Codezombie23/Bolt-Sniper/Print Files/OpticsRail/Optics Mount Lower.3mf

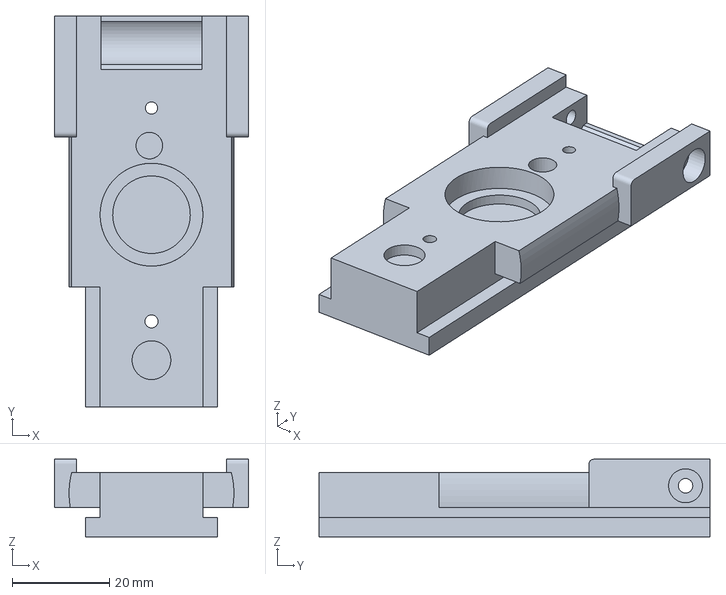
[picture p27: CAD file, 2025-10-11]
Print Files/OpticsRail/Optics Mount Lower.3mf
40.0 x 80.5 x 16.0 mm
