Codezombie23/Bolt-Sniper/Print Files/Receiver/Reciever RHS Double.3mf

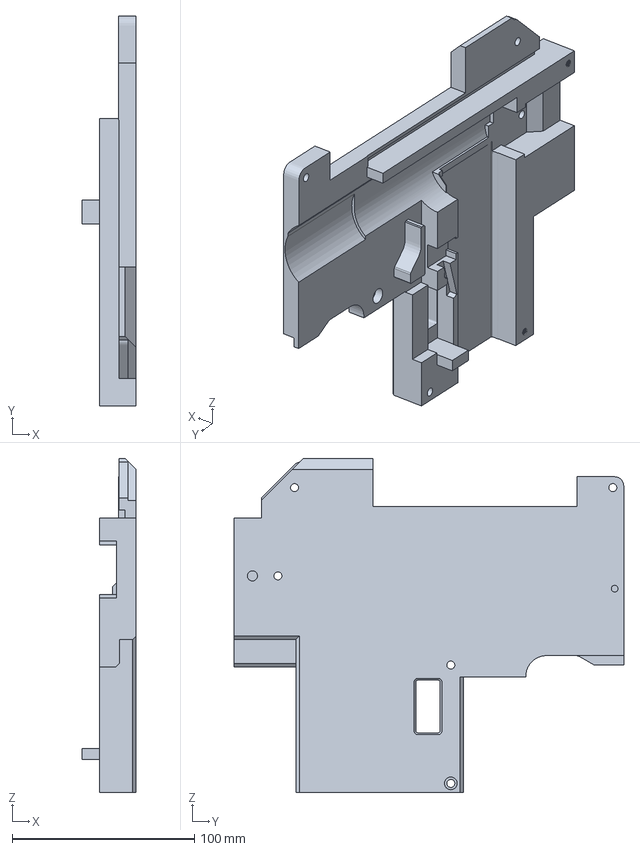
[picture p28: CAD file, 2025-10-11]
Print Files/Receiver/Reciever RHS Double.3mf
29.8 x 214.0 x 183.5 mm
