Codezombie23/Bolt-Sniper/Print Files/Shell/Stock.3mf

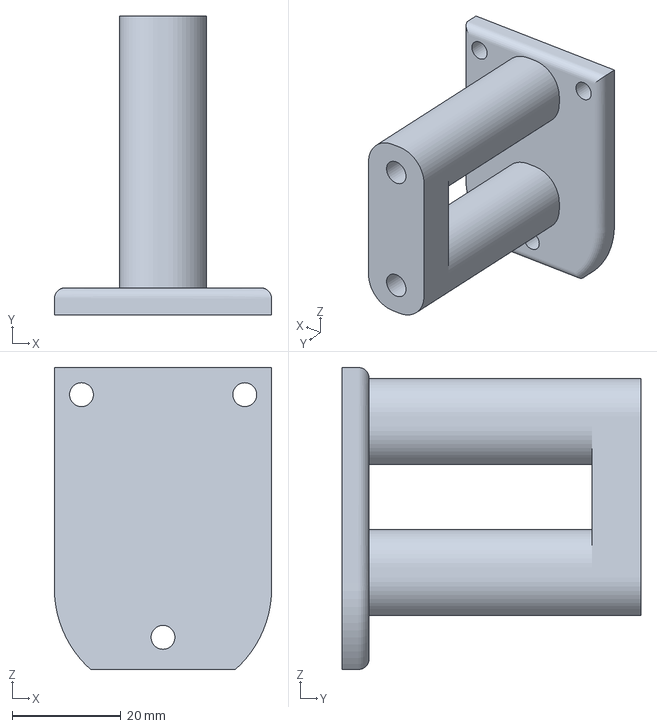
[picture p29: CAD file, 2025-10-11]
Print Files/Shell/Stock.3mf
40.0 x 55.0 x 55.6 mm
