Codezombie23/Bolt-Sniper/Print Files/Trigger Group/GripLHS (STG-44).3mf

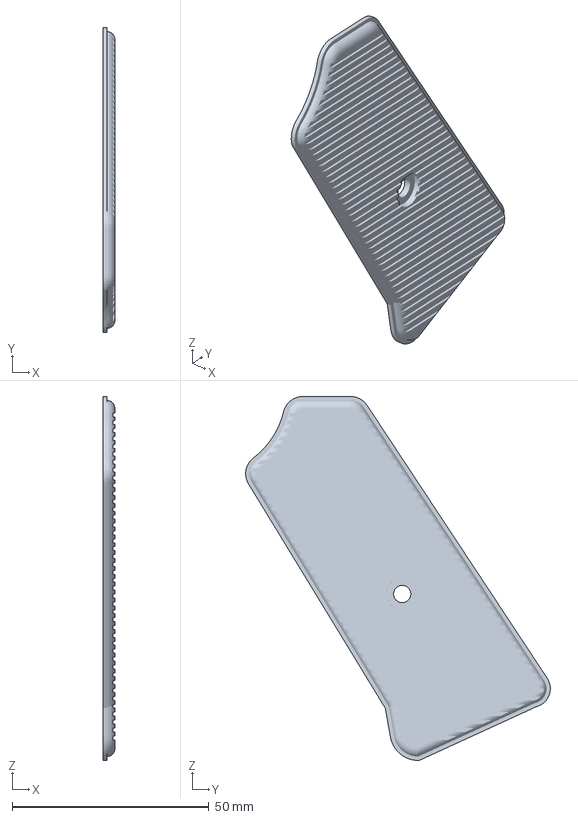
[picture p30: CAD file, 2025-10-06]
Print Files/Trigger Group/GripLHS (STG-44).3mf
3.00 x 77.4 x 92.4 mm
