Codezombie23/Bolt-Sniper/Print Files/Barrel Shroud/Barrel Shroud Front.3mf

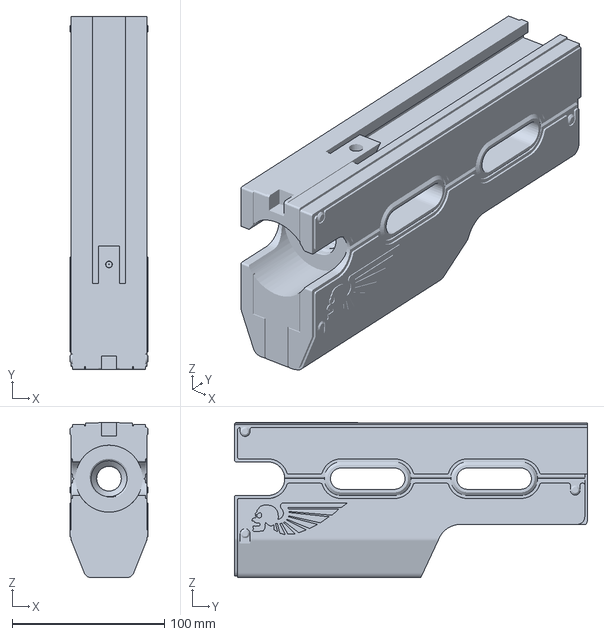
[picture p31: CAD file, 2025-10-11]
Print Files/Barrel Shroud/Barrel Shroud Front.3mf
51.0 x 231.8 x 102.0 mm
