Codezombie23/Bolt-Sniper/Print Files/Internals/Piston for 37 L1.3mf

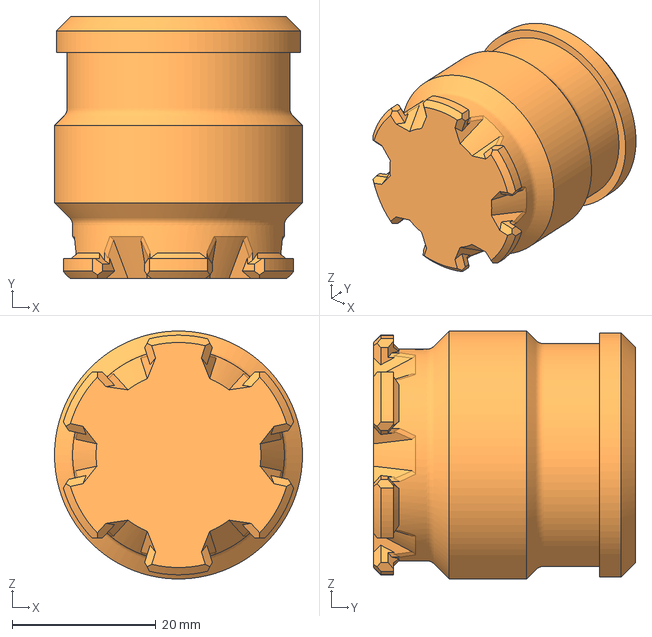
[picture p32: CAD file, 2025-10-11]
Print Files/Internals/Piston for 37 L1.3mf
34.5 x 36.5 x 34.5 mm
