Codezombie23/Bolt-Sniper/Print Files/OpticsRail/Solid OpticsMount.3mf

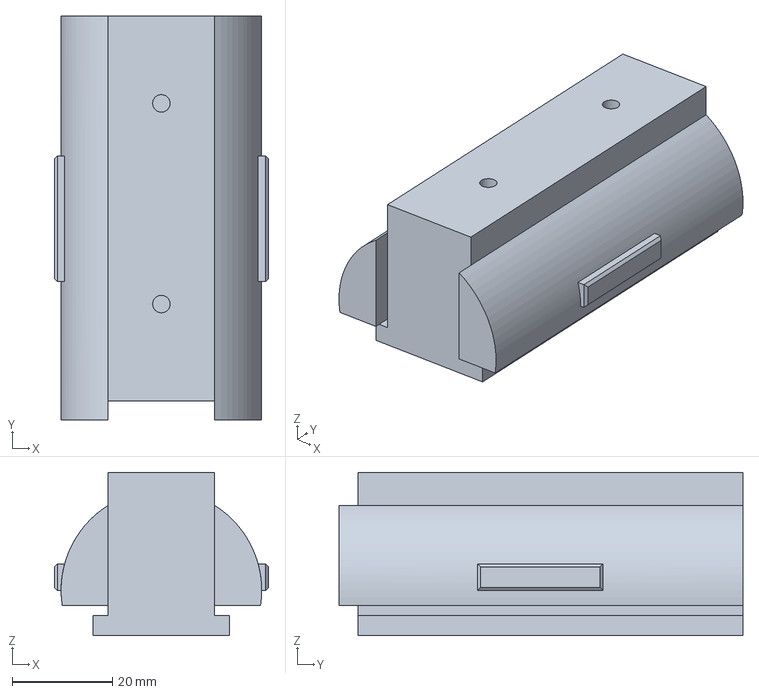
[picture p33: CAD file, 2025-10-11]
Print Files/OpticsRail/Solid OpticsMount.3mf
42.8 x 80.5 x 32.5 mm
