Codezombie23/Bolt-Sniper/Print Files/Trigger Group/Fire Group Frame Right.3mf

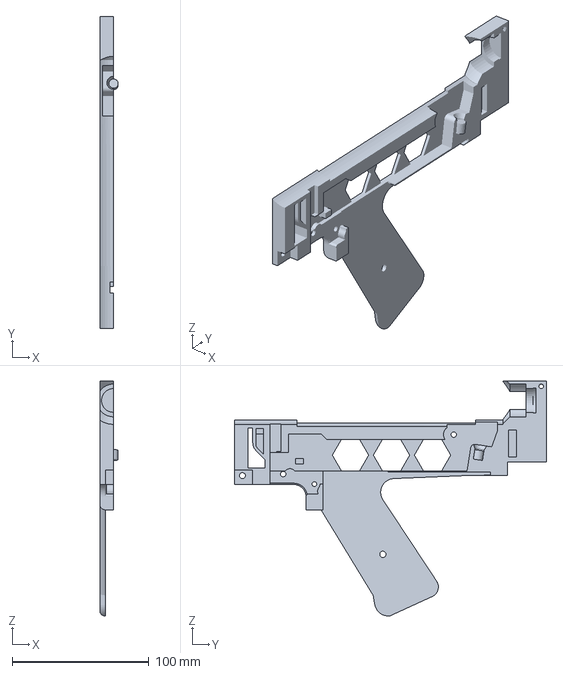
[picture p35: CAD file, 2025-10-06]
Print Files/Trigger Group/Fire Group Frame Right.3mf
13.5 x 228.5 x 171.8 mm
