Codezombie23/Bolt-Sniper/Print Files/Internals/RearShell.3mf

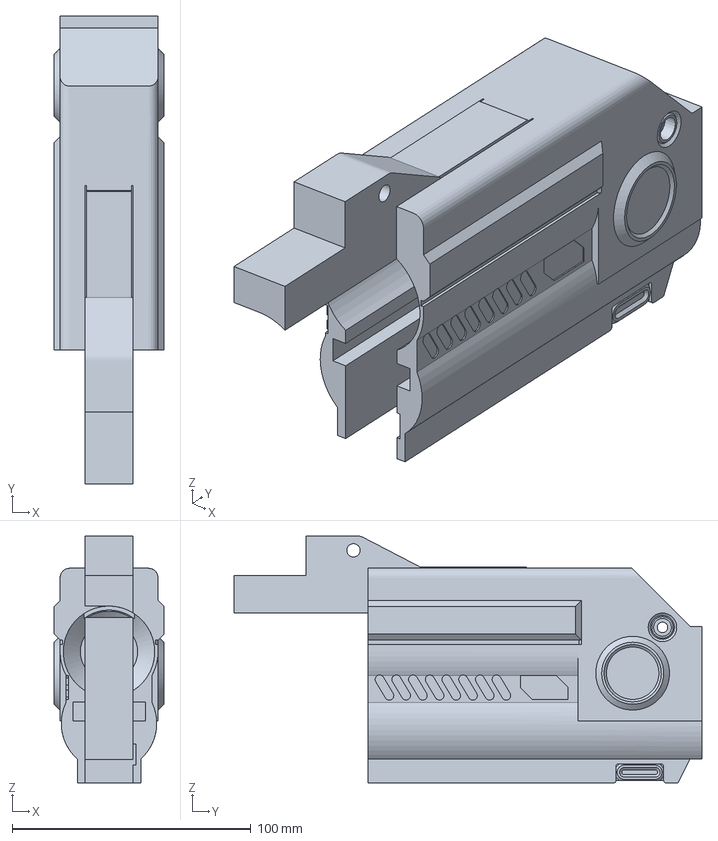
[picture p36: CAD file, 2025-10-11]
Print Files/Internals/RearShell.3mf
46.0 x 196.0 x 103.5 mm
