Codezombie23/Bolt-Sniper/Print Files/OpticsRail/Optics Thumb Wheel.3mf

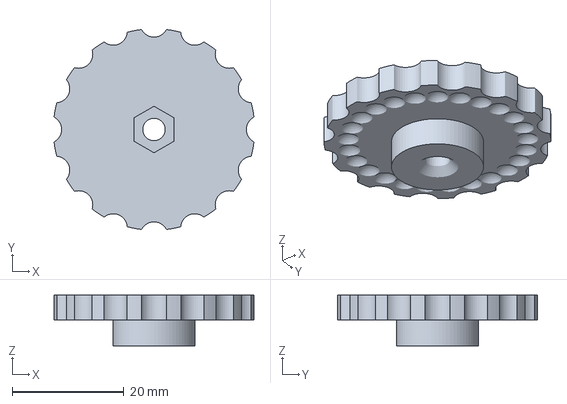
[picture p37: CAD file, 2025-10-11]
Print Files/OpticsRail/Optics Thumb Wheel.3mf
35.7 x 35.7 x 9.10 mm
