Codezombie23/Bolt-Sniper/Print Files/Receiver/Mag Release Internal.3mf

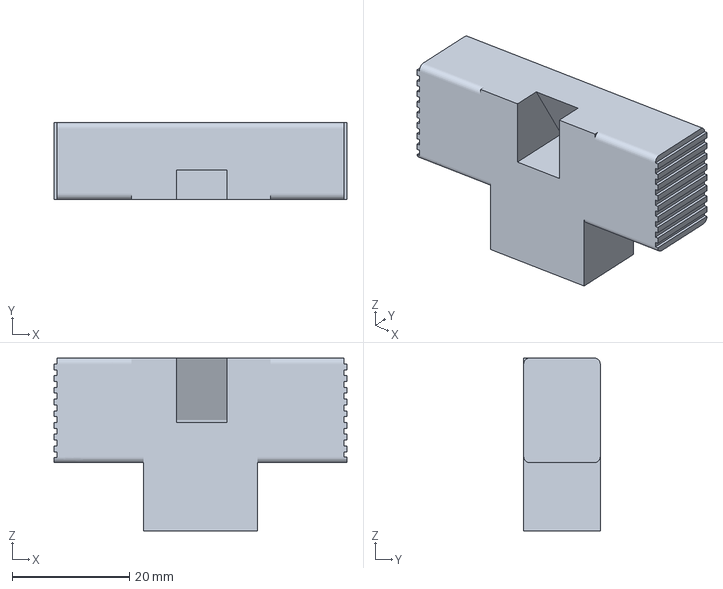
[picture p38: CAD file, 2025-10-11]
Print Files/Receiver/Mag Release Internal.3mf
50.0 x 13.1 x 29.5 mm
