Codezombie23/Bolt-Sniper/Print Files/Shell/Grip Connector.3mf

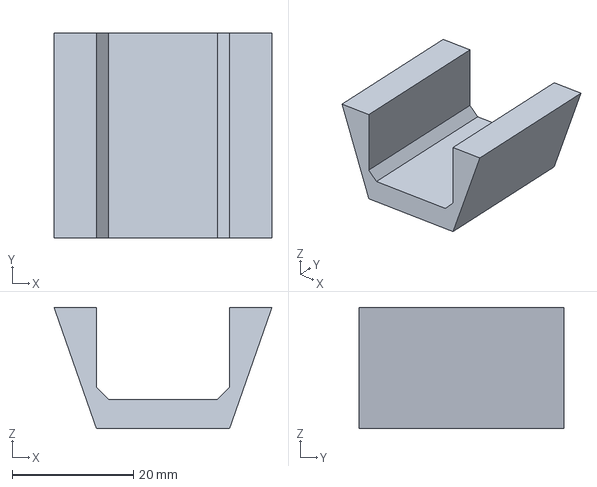
[picture p39: CAD file, 2025-10-11]
Print Files/Shell/Grip Connector.3mf
36.0 x 33.8 x 20.0 mm
