Codezombie23/Bolt-Sniper/Print Files/Trigger Group/Grip Frame.3mf

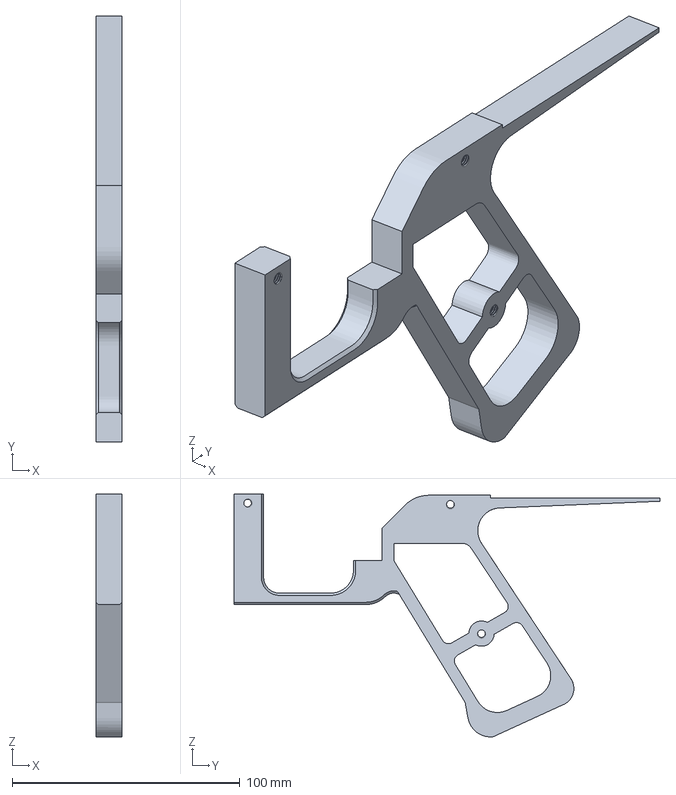
[picture p40: CAD file, 2025-10-06]
Print Files/Trigger Group/Grip Frame.3mf
11.2 x 187.0 x 106.6 mm
