Codezombie23/Bolt-Sniper/Print Files/Internals/Charging Handle.3mf

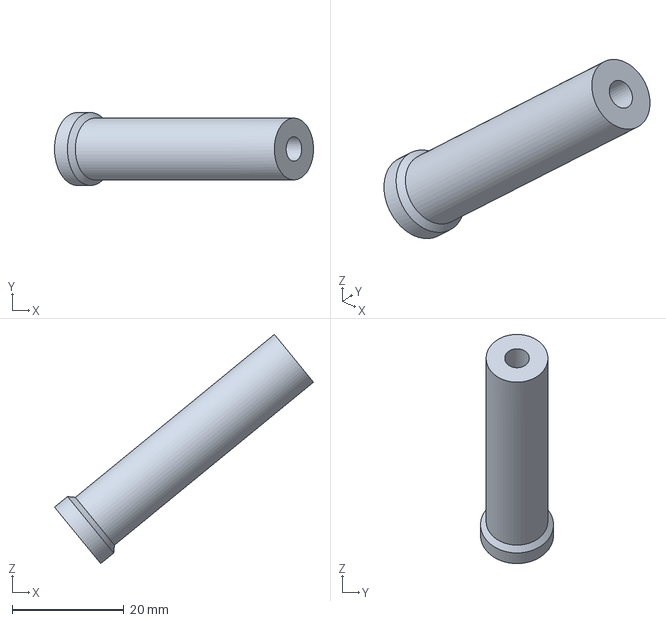
[picture p41: CAD file, 2025-10-11]
Print Files/Internals/Charging Handle.3mf
46.3 x 13.1 x 41.0 mm
