Codezombie23/Bolt-Sniper/Print Files/OpticsRail/Optics Mount Upper.3mf

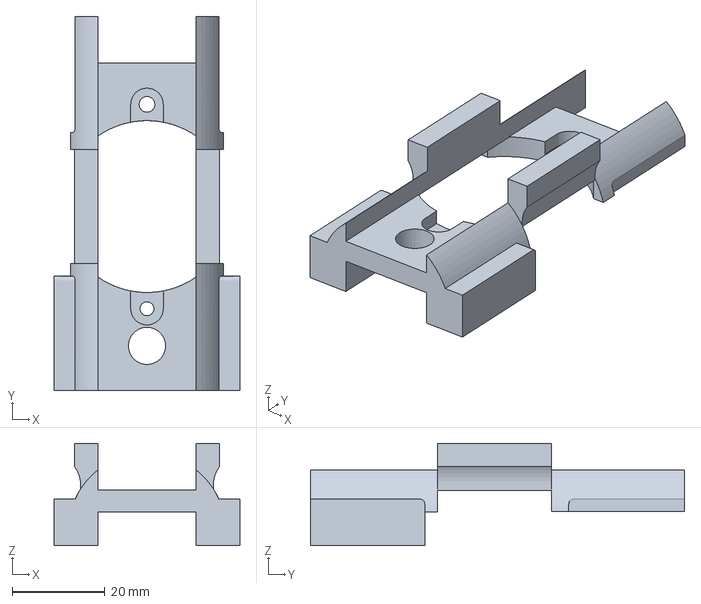
[picture p42: CAD file, 2025-10-11]
Print Files/OpticsRail/Optics Mount Upper.3mf
40.0 x 80.5 x 22.0 mm
