Codezombie23/Bolt-Sniper/Print Files/Receiver/Reciever LHS Double.3mf

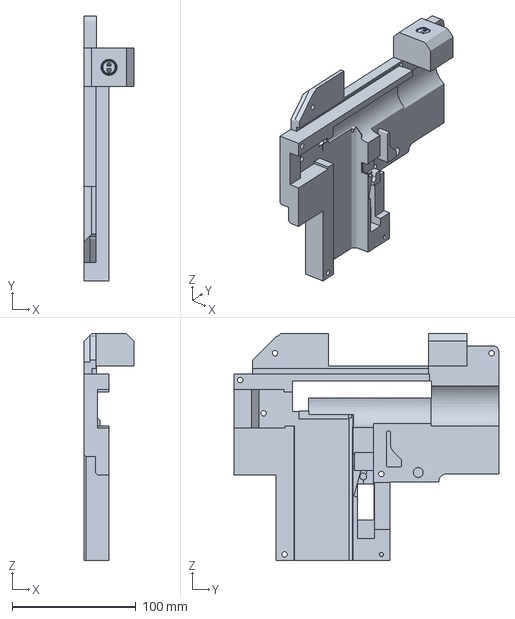
[picture p43: CAD file, 2025-10-11]
Print Files/Receiver/Reciever LHS Double.3mf
40.0 x 214.0 x 183.5 mm
