Codezombie23/Bolt-Sniper/Print Files/Shell/SidePanel LHS.3mf

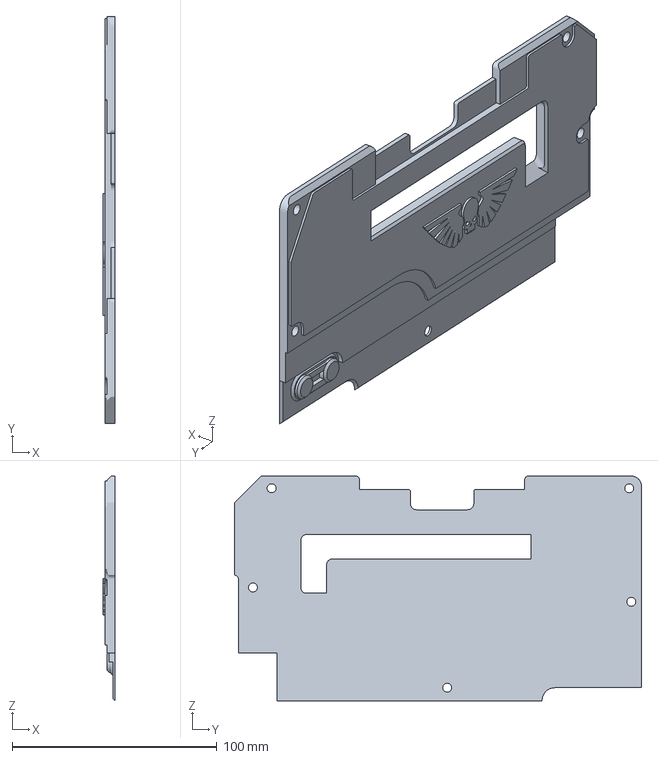
[picture p44: CAD file, 2025-10-11]
Print Files/Shell/SidePanel LHS.3mf
6.00 x 199.0 x 110.0 mm
