Codezombie23/Bolt-Sniper/Print Files/Trigger Group/Grip Locator.3mf

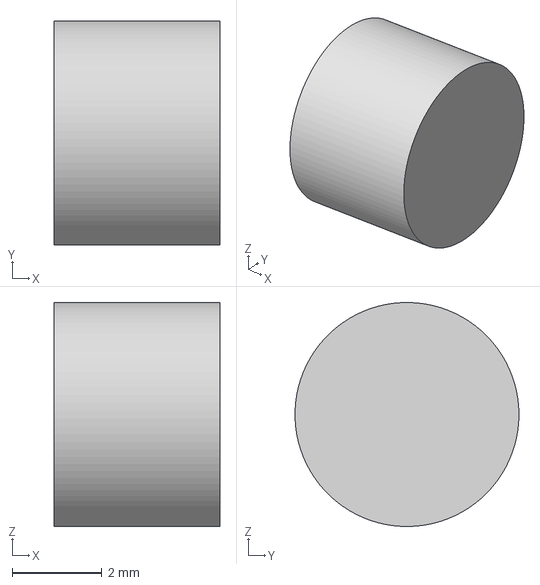
[picture p45: CAD file, 2025-10-06]
Print Files/Trigger Group/Grip Locator.3mf
3.70 x 5.00 x 5.00 mm
