Codezombie23/Bolt-Sniper/Print Files/OpticsRail/Locator.3mf

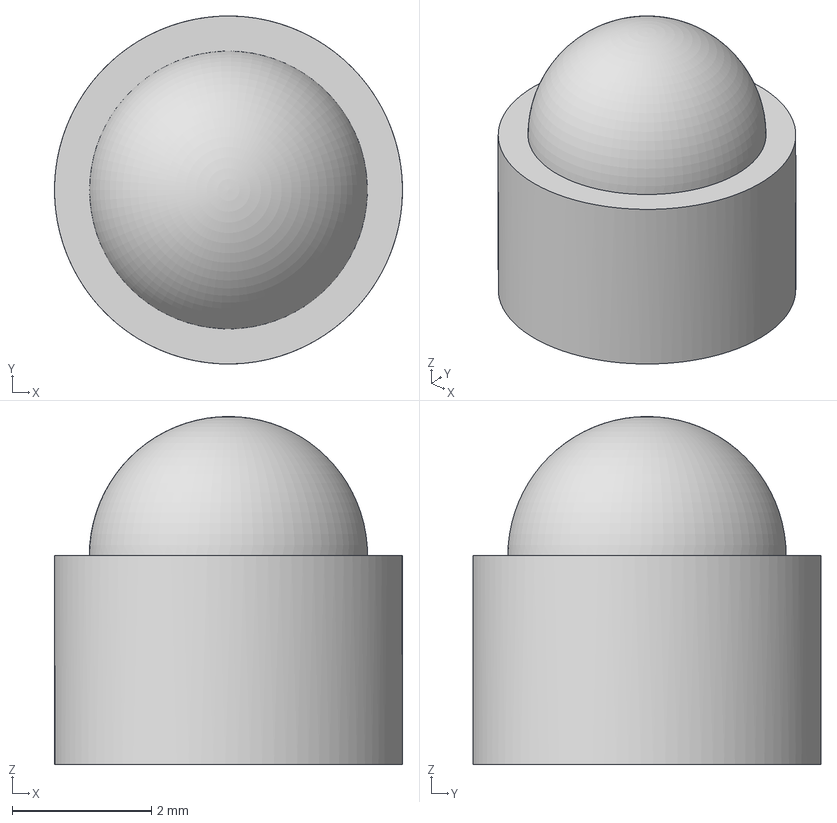
[picture p46: CAD file, 2025-10-11]
Print Files/OpticsRail/Locator.3mf
5.00 x 5.00 x 5.00 mm
