Codezombie23/Bolt-Sniper/Print Files/Receiver/MagReleaseBarDouble.3mf

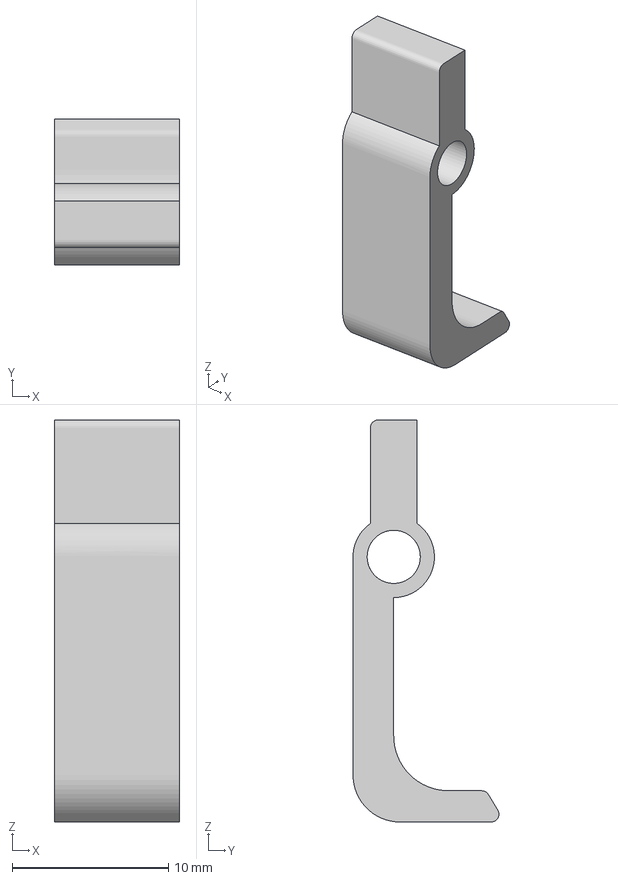
[picture p47: CAD file, 2025-10-11]
Print Files/Receiver/MagReleaseBarDouble.3mf
8.00 x 9.33 x 25.7 mm
