Codezombie23/Bolt-Sniper/Print Files/Trigger Group/Spring Holder.3mf

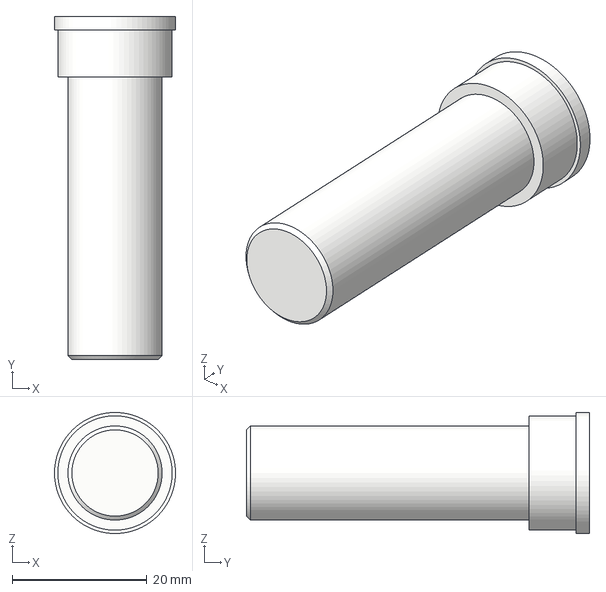
[picture p48: CAD file, 2025-10-06]
Print Files/Trigger Group/Spring Holder.3mf
18.0 x 51.0 x 18.0 mm
