Codezombie23/Bolt-Sniper/Print Files/Trigger Group/TransferBar.3mf

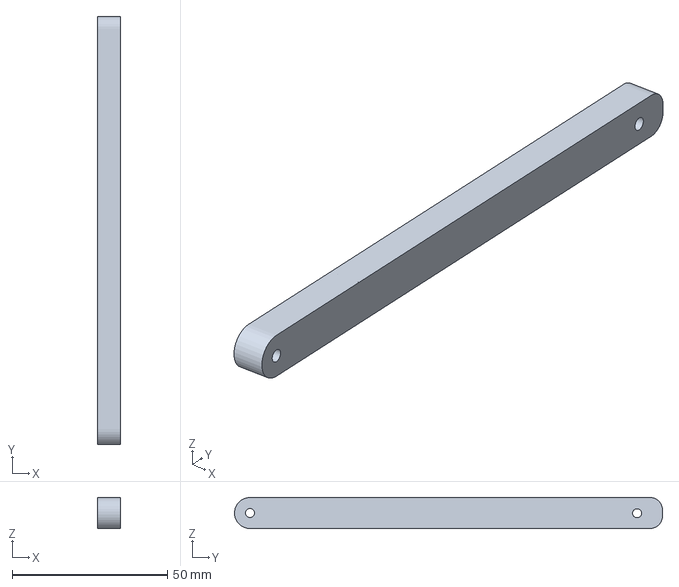
[picture p49: CAD file, 2025-10-06]
Print Files/Trigger Group/TransferBar.3mf
7.50 x 137.9 x 10.0 mm
