Codezombie23/Bolt-Sniper/Print Files/Receiver/MagReleaseDouble.3mf

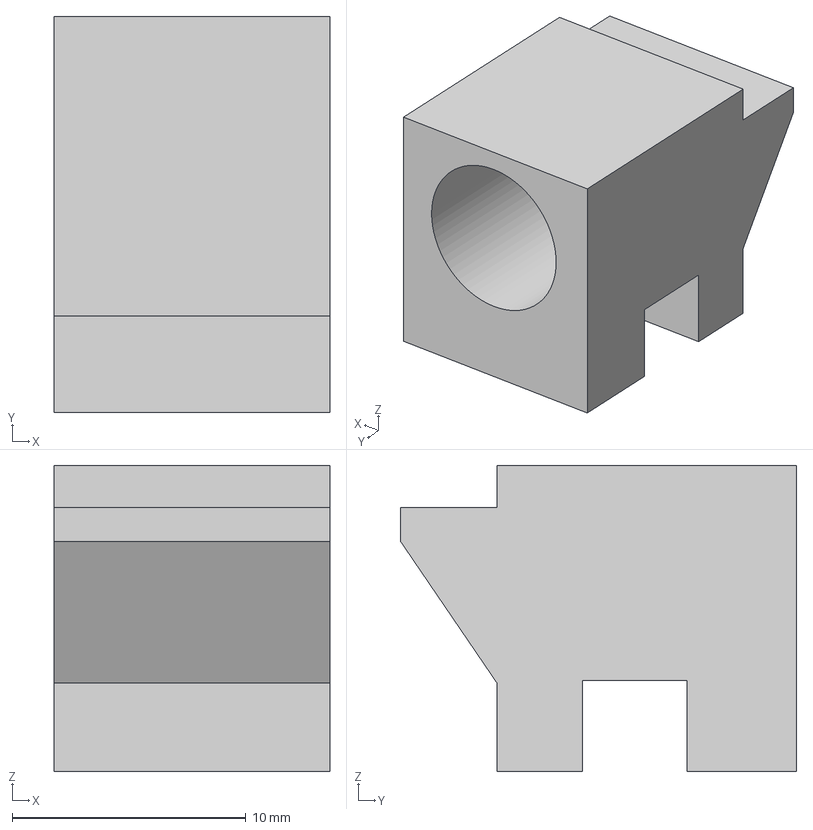
[picture p50: CAD file, 2025-10-11]
Print Files/Receiver/MagReleaseDouble.3mf
11.8 x 17.0 x 13.1 mm
