Codezombie23/Bolt-Sniper/Print Files/Shell/Stock Pad.3mf

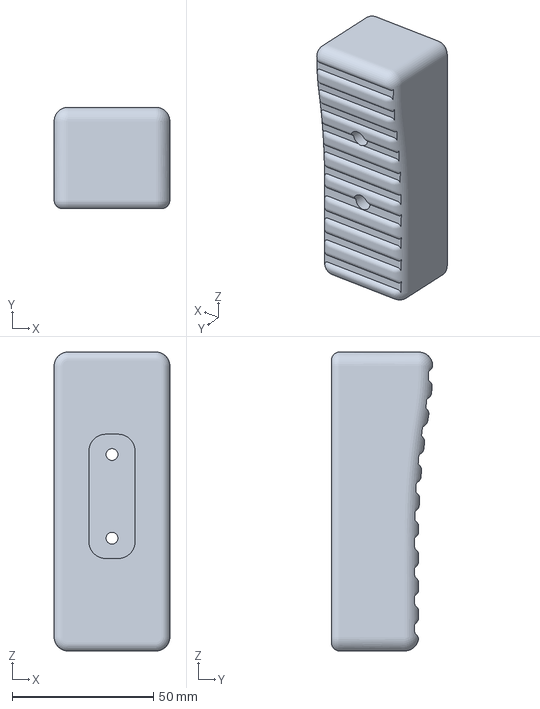
[picture p51: CAD file, 2025-10-11]
Print Files/Shell/Stock Pad.3mf
41.0 x 36.0 x 106.0 mm
