Codezombie23/Bolt-Sniper/Print Files/Trigger Group/Trigger.3mf

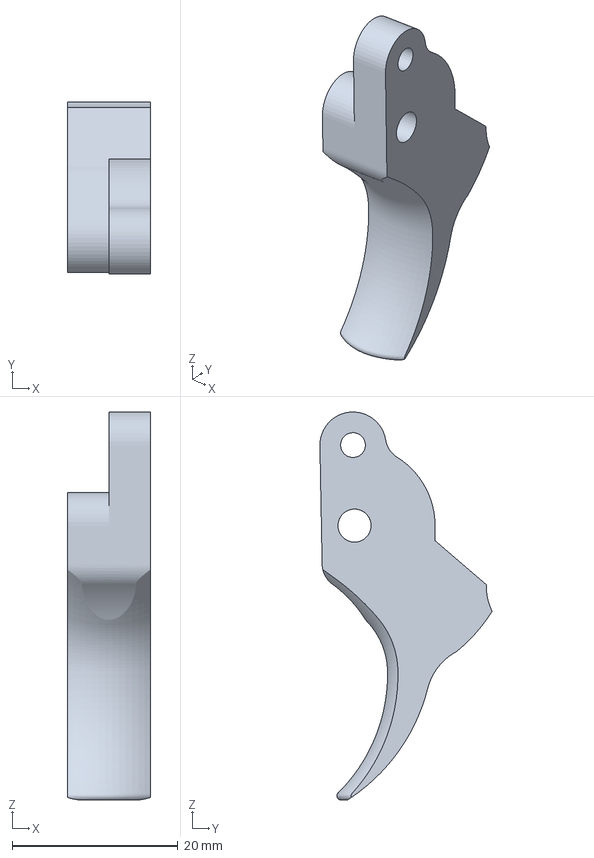
[picture p52: CAD file, 2025-10-06]
Print Files/Trigger Group/Trigger.3mf
10.00 x 20.8 x 46.9 mm
