Codezombie23/Bolt-Sniper/Print Files/Trigger Group/GripRHS (STG-44).3mf

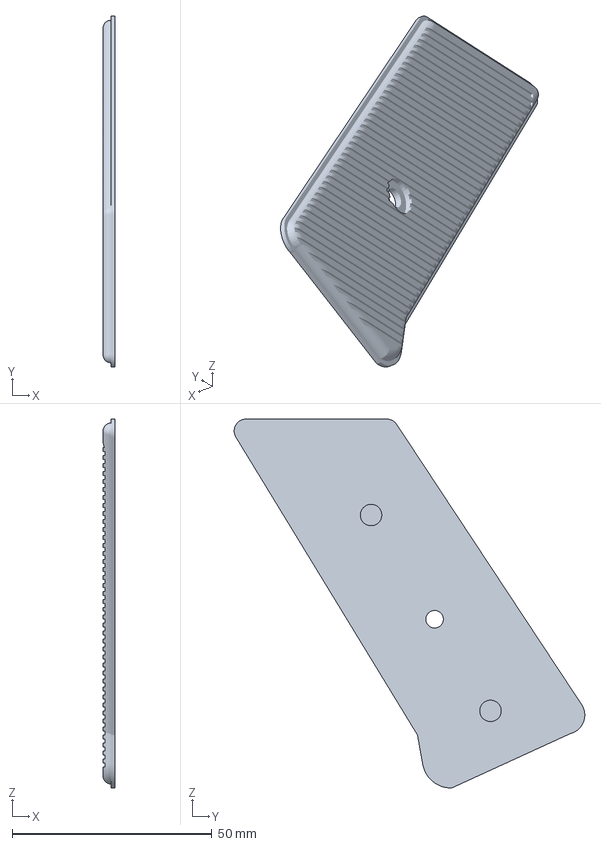
[picture p53: CAD file, 2025-10-06]
Print Files/Trigger Group/GripRHS (STG-44).3mf
3.00 x 87.8 x 92.4 mm
