Codezombie23/Bolt-Sniper/Print Files/Trigger Group/Fire Group Frame Left.3mf

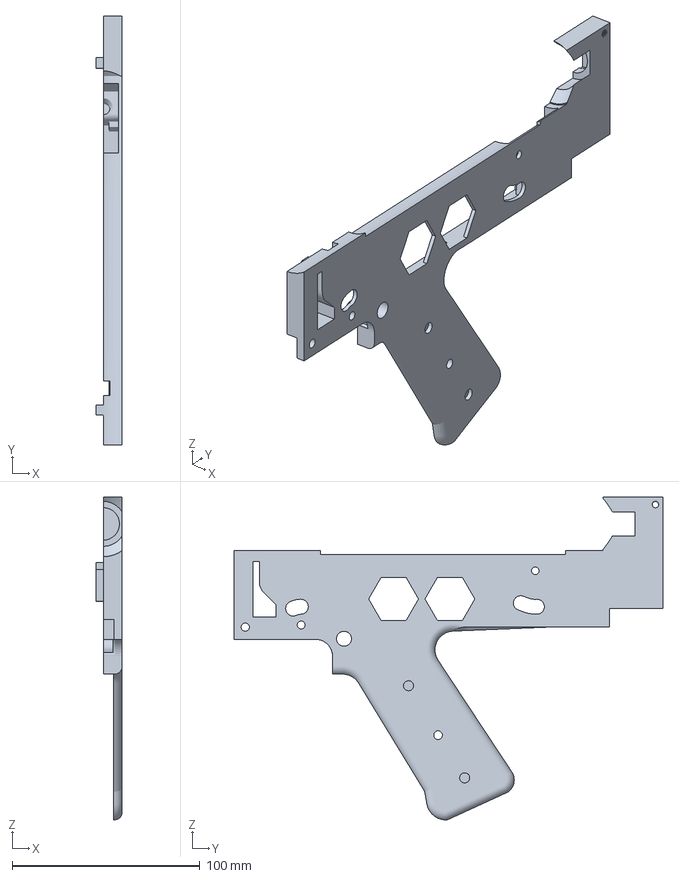
[picture p54: CAD file, 2025-10-06]
Print Files/Trigger Group/Fire Group Frame Left.3mf
14.0 x 228.5 x 171.8 mm
