Codezombie23/Bolt-Sniper/Print Files/Trigger Group/Sear.3mf

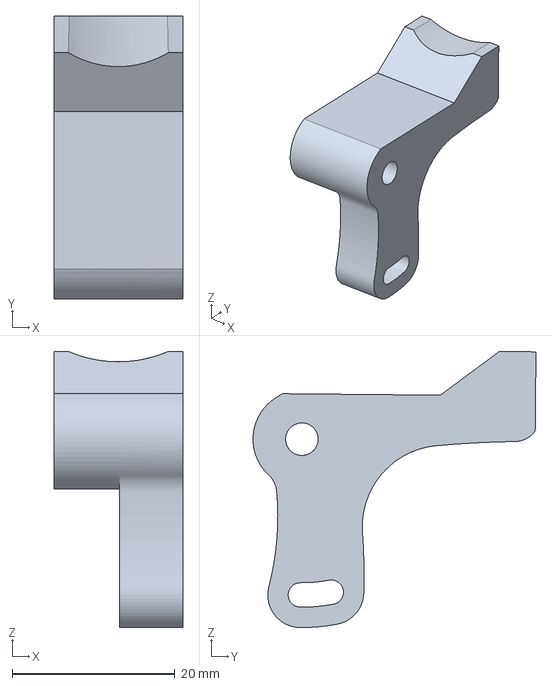
[picture p55: CAD file, 2025-10-06]
Print Files/Trigger Group/Sear.3mf
15.8 x 34.7 x 33.9 mm
